danielzyy/Smart_Lamp/Circuit Schematic/smart_lamp_circuit.kicad_sch

## KiCad design Circuit Schematic/smart_lamp_circuit.kicad_sch (2022-08-29)

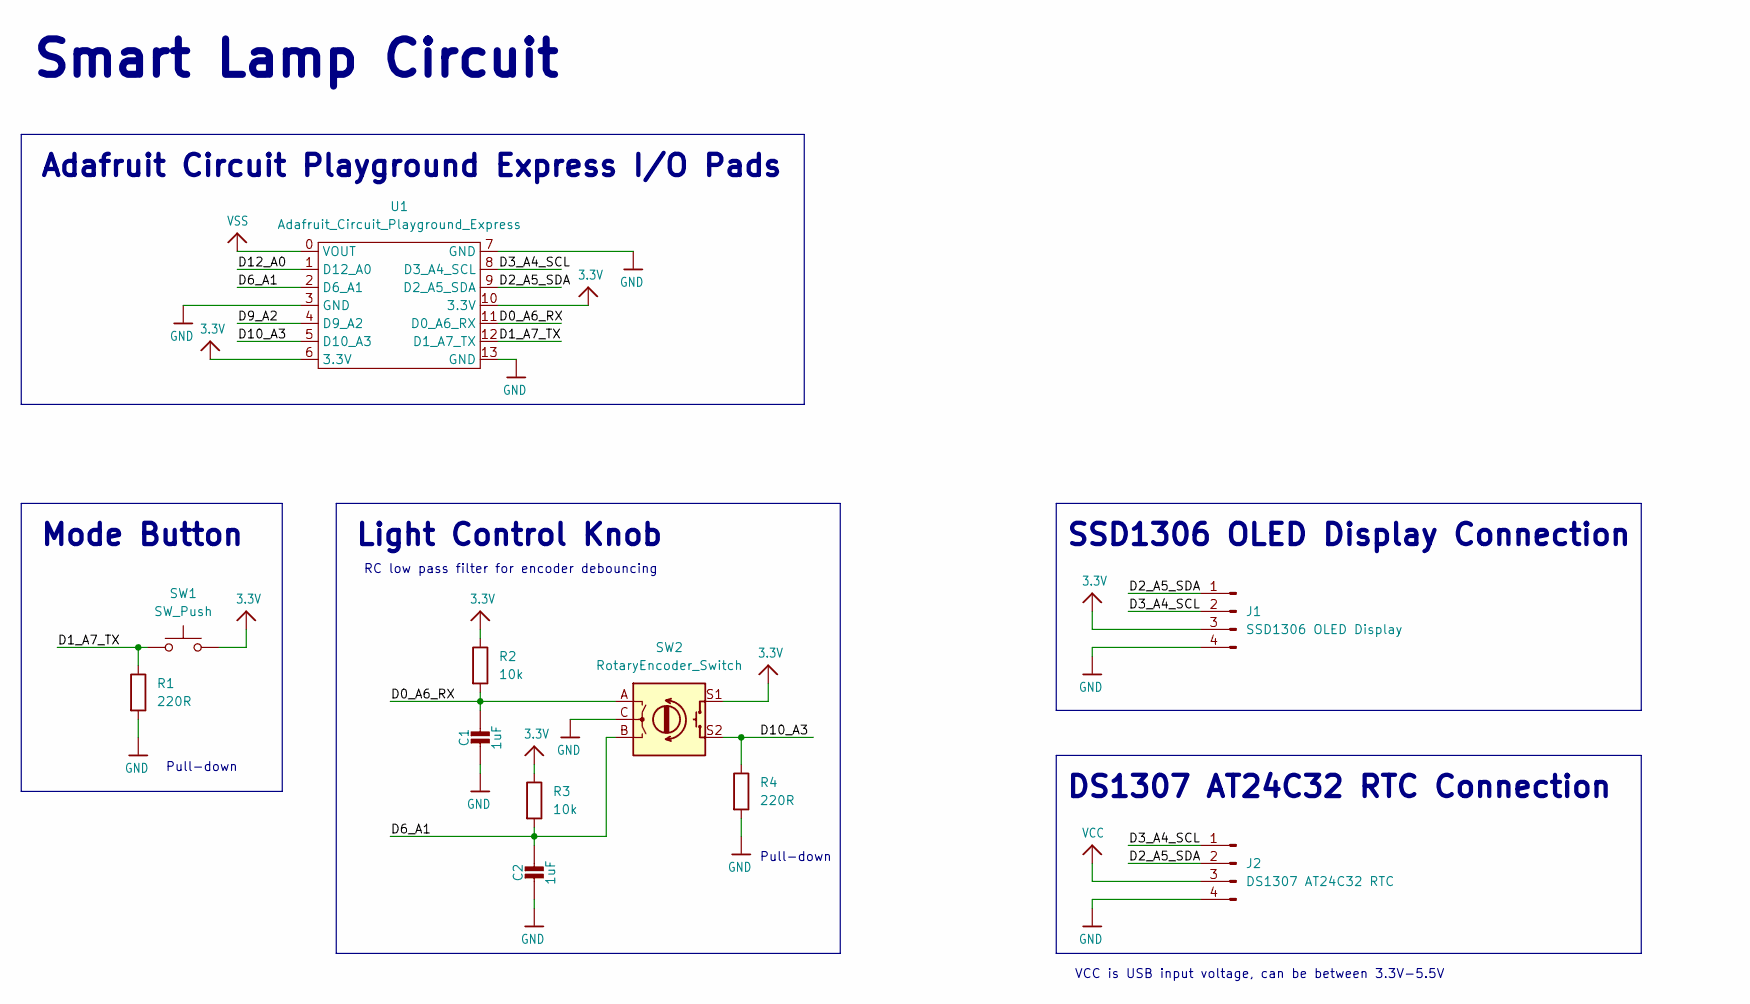
[picture p11: schematic smart_lamp_circuit.kicad_sch]

Parts:
C1, C2: 1uF; 0603-NO
J1: SSD1306 OLED Display
J2: DS1307 AT24C32 RTC
R1, R4: 220R
R2, R3: 10k
SW1: SW_Push
SW2: RotaryEncoder_Switch
U1: Adafruit_Circuit_Playground_Express

Connections:
3.3V: J1.3, R2.1, R3.1, SW1.2, SW2.S1, U1.6 (3.3V), U1.10 (3.3V)
D0_A6_RX: C1.1, R2.2, SW2.A, U1.11 (D0_A6_RX)
D1_A7_TX: R1.1, SW1.1, U1.12 (D1_A7_TX)
D2_A5_SDA: J1.1, J2.2, U1.9 (D2_A5_SDA)
D3_A4_SCL: J1.2, J2.1, U1.8 (D3_A4_SCL)
D6_A1: C2.1, R3.2, SW2.B, U1.2 (D6_A1)
D9_A2: U1.4 (D9_A2)
D10_A3: R4.1, SW2.S2, U1.5 (D10_A3)
D12_A0: U1.1 (D12_A0)
GND: C1.2, C2.2, J1.4, J2.4, R1.2, R4.2, SW2.C, U1.3 (GND), U1.7 (GND), U1.13 (GND)
VCC: J2.3
VSS: U1.0 (VOUT)

Notes on the sheet:
Adafruit Circuit Playground Express I/O Pads
Pull-down
RC low pass filter for encoder debouncing
Light Control Knob
DS1307 AT24C32 RTC Connection
Smart Lamp Circuit
VCC is USB input voltage, can be between 3.3V-5.5V
Mode Button
SSD1306 OLED Display Connection
